robertgallup/arduino-DualLFO/DUAL_LFO/pulse16.h

/////////////////////////////////////////////////////
//
//  256-byte Pulse Wave (16-byte pulse)
//
//  The MIT License (MIT)
//  
//  Copyright (c) 2013 Robert W. Gallup (www.robertgallup.com)
//  
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

PROGMEM byte pulse16[] = {

	255,	     // 0
	255,	     // 1
	255,	     // 2
	255,	     // 3
	255,	     // 4
	255,	     // 5
	255,	     // 6
	255,	     // 7
	255,	     // 8
	255,	     // 9
	255,	     // 10
	255,	     // 11
	255,	     // 12
	255,	     // 13
	255,	     // 14
	255,	     // 15
	0,	     // 16
	0,	     // 17
	0,	     // 18
	0,	     // 19
	0,	     // 20
	0,	     // 21
	0,	     // 22
	0,	     // 23
	0,	     // 24
	0,	     // 25
	0,	     // 26
	0,	     // 27
	0,	     // 28
	0,	     // 29
	0,	     // 30
	0,	     // 31
	0,	     // 32
	0,	     // 33
	0,	     // 34
	0,	     // 35
	0,	     // 36
	0,	     // 37
	0,	     // 38
	0,	     // 39
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
};
