robertgallup/arduino-DualLFO/DUAL_LFO/noise256.h

/////////////////////////////////////////////////////
//
//  Positive 256-byte Noise Wave
//
//  The MIT License (MIT)
//  
//  Copyright (c) 2013 Robert W. Gallup (www.robertgallup.com)
//  
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

PROGMEM byte noise256[] ={

	79,	     // 0
	182,	     // 1
	29,	     // 2
	52,	     // 3
	110,	     // 4
	86,	     // 5
	105,	     // 6
	231,	     // 7
	46,	     // 8
	120,	     // 9
	31,	     // 10
	78,	     // 11
	238,	     // 12
	143,	     // 13
	170,	     // 14
	20,	     // 15
	6,	     // 16
	43,	     // 17
	118,	     // 18
	153,	     // 19
	244,	     // 20
	29,	     // 21
	29,	     // 22
	148,	     // 23
	211,	     // 24
	20,	     // 25
	96,	     // 26
	111,	     // 27
	236,	     // 28
	38,	     // 29
	205,	     // 30
	6,	     // 31
	171,	     // 32
	249,	     // 33
	13,	     // 34
	3,	     // 35
	211,	     // 36
	30,	     // 37
	20,	     // 38
	139,	     // 39
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

};
