robertgallup/arduino-DualLFO/DUAL_LFO/saw256.h

/////////////////////////////////////////////////////
//
// Positive 256-byte Sawtooth Wave
//
//  The MIT License (MIT)
//  
//  Copyright (c) 2013 Robert W. Gallup (www.robertgallup.com)
//  
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

PROGMEM byte saw256[] = {

	255,	     // 0
	254,	     // 1
	253,	     // 2
	252,	     // 3
	251,	     // 4
	250,	     // 5
	249,	     // 6
	248,	     // 7
	247,	     // 8
	246,	     // 9
	245,	     // 10
	244,	     // 11
	243,	     // 12
	242,	     // 13
	241,	     // 14
	240,	     // 15
	239,	     // 16
	238,	     // 17
	237,	     // 18
	236,	     // 19
	235,	     // 20
	234,	     // 21
	233,	     // 22
	232,	     // 23
	231,	     // 24
	230,	     // 25
	229,	     // 26
	228,	     // 27
	227,	     // 28
	226,	     // 29
	225,	     // 30
	224,	     // 31
	223,	     // 32
	222,	     // 33
	221,	     // 34
	220,	     // 35
	219,	     // 36
	218,	     // 37
	217,	     // 38
	216,	     // 39
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

};
