robertgallup/arduino-DualLFO/DUAL_LFO/sine256.h

/////////////////////////////////////////////////////
//
// Positive 256-byte Sine Wave
//
//  The MIT License (MIT)
//  
//  Copyright (c) 2013 Robert W. Gallup (www.robertgallup.com)
//  
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

PROGMEM byte sine256[] ={

	128,	     // 0
	131,	     // 1
	134,	     // 2
	137,	     // 3
	140,	     // 4
	143,	     // 5
	146,	     // 6
	149,	     // 7
	153,	     // 8
	156,	     // 9
	159,	     // 10
	162,	     // 11
	165,	     // 12
	168,	     // 13
	171,	     // 14
	174,	     // 15
	177,	     // 16
	180,	     // 17
	182,	     // 18
	185,	     // 19
	188,	     // 20
	191,	     // 21
	194,	     // 22
	196,	     // 23
	199,	     // 24
	201,	     // 25
	204,	     // 26
	207,	     // 27
	209,	     // 28
	211,	     // 29
	214,	     // 30
	216,	     // 31
	218,	     // 32
	220,	     // 33
	223,	     // 34
	225,	     // 35
	227,	     // 36
	229,	     // 37
	231,	     // 38
	232,	     // 39
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

};
