robertgallup/arduino-DualLFO/DUAL_LFO/tri256.h

/////////////////////////////////////////////////////
//
// Positive 256-byte Triangle Wave
//
//  The MIT License (MIT)
//  
//  Copyright (c) 2013 Robert W. Gallup (www.robertgallup.com)
//  
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

PROGMEM byte tri256[] ={

	128,	     // 0
	130,	     // 1
	132,	     // 2
	134,	     // 3
	136,	     // 4
	138,	     // 5
	140,	     // 6
	142,	     // 7
	144,	     // 8
	146,	     // 9
	148,	     // 10
	150,	     // 11
	152,	     // 12
	154,	     // 13
	156,	     // 14
	158,	     // 15
	160,	     // 16
	162,	     // 17
	164,	     // 18
	166,	     // 19
	168,	     // 20
	170,	     // 21
	172,	     // 22
	174,	     // 23
	176,	     // 24
	178,	     // 25
	180,	     // 26
	182,	     // 27
	184,	     // 28
	186,	     // 29
	188,	     // 30
	190,	     // 31
	192,	     // 32
	194,	     // 33
	196,	     // 34
	198,	     // 35
	200,	     // 36
	202,	     // 37
	204,	     // 38
	206,	     // 39
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

};
